DevOpsOfChaos/smarthome-technikerprojekt/docs/firmware/devices/README.md

# Devices — Übersicht

| Device | Datei | Kurzbeschreibung |
|---|---|---|
| NET-ERL-001 | [NET-ERL-001_hall_module.md](NET-ERL-001_hall_module.md) | Flurmodul (PIR, BME280, VEML7700, 1 Relais) |
| NET-ERL-002 | [NET-ERL-002_hall_module_led_ring.md](NET-ERL-002_hall_module_led_ring.md) | Erweitertes Flurmodul (LD2410 Radar, BME680, ENS160, NeoPixel-Ring, 1 Relais) |
| NET-ZRL-002 | [NET-ZRL-002_shutter_module.md](NET-ZRL-002_shutter_module.md) | Rollladenmodul (2 Relais, 3 Taster, Kalibrierung, Positionsschätzung) |
| NET-SEN-002 | [NET-SEN-002_weather_station.md](NET-SEN-002_weather_station.md) | Wettersensor (BME280, VEML7700, digitaler Regen) |
| bat_sen_01 | [bat_sen_01_window_contact.md](bat_sen_01_window_contact.md) | Batterie-Fensterkontakt (Reed, 2x AAA, GPIO-Wake) |
| bat_sen_02 | [bat_sen_02_rain_sensor.md](bat_sen_02_rain_sensor.md) | Batterie-Regensensor (ADC, Hysterese, Timer-Wake) |
