DevOpsOfChaos/smarthome-technikerprojekt/firmware/src/basetypes/master_firmware/README.md

# Master Firmware

Basistyp fuer die zentrale ESP-NOW-zu-MQTT-Bruecke.

Basis:
- Dynamische Node-Registry fuer Netz- und Batterie-Nodes
- ESP-NOW-Empfang fuer HELLO, HEARTBEAT, STATE, EVENT und ACK
- ESP-NOW-Senden fuer HELLO_ACK, STATE_REQUEST, CMD und CFG
- MQTT-Ausgabe fuer Master-Status, Node-Meta, Availability, State, Event und ACK
- MQTT-Kommandos fuer `get_state`, `set_relay`, `set_config`, `open`, `close`, `stop` und `set_position`
- Pending-/Retry-Logik fuer bestaetigungspflichtige CMD- und CFG-Nachrichten

Sichtbare MQTT-Linie:
- `smarthome/master/{DEVICE_ID}/status`
- `smarthome/master/{DEVICE_ID}/event`
- `smarthome/device/{node_id}/meta`
- `smarthome/device/{node_id}/availability`
- `smarthome/device/{node_id}/state`
- `smarthome/device/{node_id}/ack`
- `smarthome/device/{node_id}/event`
- `smarthome/device/{node_id}/command`

Hinweis:
- Zugangsdaten gehoeren nicht in diese Firmware-Dateien, sondern in die lokale `Secrets.h`.
- Der Master speichert keine feste Node-Liste; Nodes melden sich dynamisch per HELLO.
- `HELLO` ist die einzige Quelle fuer `device_class`, `power_type`, `caps` und Profile.
- Wenn zuerst nur `HEARTBEAT` oder `STATE` einer unbekannten Node eintrifft, legt der Master nur einen provisorischen Slot fuer `device_id` und MAC an, sendet `HELLO_REQUEST` und wartet. Er leitet keine Geraeteklasse aus ID-Praefixen oder Payload-Laengen ab; Availability meldet den Versorgungstyp bis zum HELLO als `unknown`.
- Batterie-Nodes duerfen laenger schlafen als Netz-Nodes. Der Master nutzt fuer BAT-SEN das gemeldete `report_interval_s`; ohne diesen Wert gilt ein konservativer Mindest-Timeout von 25min.
- NET-SEN-Regenereignisse werden zusaetzlich in den retained `state` gespiegelt (`rain`), damit ein trocken/nass-Wechsel nicht nur als fluechtiges Event sichtbar ist.
