DevOpsOfChaos/smarthome-technikerprojekt/hardware/bat_sen/devices/bat_sen_01_window_contact/gefertigte_Platine/README.md

# bat_sen_01 — KiCAD-Projekt (Geräte-Kopie)

> Kopie der Basetype-KiCAD-Dateien zur gerätespezifischen Anpassung.

## Enthaltene Platinen

| Platine | Quelle |
|---|---|
| [kicad/](.) | Sensor_Batteriebetrieb (Power-Gating, Batterie-ADC) |

## Anpassungen für bat_sen_01

- [ ] Reed-Schalter an GPIO3 (Wake-Up-fähig)
- [ ] 2x-AAA-Batteriehalter (BAT_PROFILE_2X_AAA)
- [ ] Keine I²C-Sensoren (JP1/JP2 offen)
