DevOpsOfChaos/smarthome-technikerprojekt/hardware/bat_sen/devices/bat_sen_02_rain_sensor-unfinished/kicad/README.md

# bat_sen_02 — KiCAD-Projekt (Geräte-Kopie)

> Kopie der Basetype-KiCAD-Dateien zur gerätespezifischen Anpassung.

## Enthaltene Platinen

| Platine | Quelle |
|---|---|
| [kicad/](.) | Sensor_Batteriebetrieb (Power-Gating, Batterie-ADC) |

## Anpassungen für bat_sen_02

- [ ] Analoger Regensensor an GPIO4 (ADC)
- [ ] 2× AA-Batteriehalter (BAT_PROFILE_2X_AA)
- [ ] Hysterese-Schwellwerte in Firmware
