DevOpsOfChaos/smarthome-technikerprojekt/hardware/3d_models/net_sen/link.txt

https://makerworld.com/de/models/1312159-modern-weather-station?from=search#profileId-1346594
