DevOpsOfChaos/smarthome-technikerprojekt/docs/public/01_projektueberblick.md

# Projektüberblick

## Ziel des Projekts
Dieses Projekt ist ein lokales, modulares Smart-Home-System im Rahmen eines Technikerprojekts.

Der Fokus liegt auf:
- klarer technischer Architektur
- nachvollziehbarer Trennung der Kommunikationswege
- wiederverwendbaren Basistypen
- sauber dokumentierter Entwicklung
- einem System, das technisch erklärbar und praktisch testbar bleibt
- einer nachvollziehbaren Wahl zwischen eigener Firmware und ESPHome-Alternative

## Systemidee in Kurzform
Die Hauptlinie des Gesamtsystems besteht aus drei Schichten:

1. **Dezentrale Geräte**
   - Sensor- und Aktormodule auf ESP32-Basis
   - Kommunikation mit dem Master ausschließlich per ESP-NOW

2. **Master**
   - zentrale Brücke zwischen Geräteschicht und Server
   - einzige Stelle, die ESP-NOW und MQTT verbindet

3. **Server**
   - MQTT-Ingest
   - Node-RED-basierte Verarbeitung und Visualisierung
   - Snapshot-Datenhaltung für aktuelle Zustände
   - Dashboard für Übersicht, Details und einfache Bedienung

Zusätzlich gibt es eine ESPHome-Alternative:
- Geräte werden in ESPHome/YAML beschrieben
- Home Assistant beziehungsweise ESPHome baut und flasht die Geräte
- die Geräte sprechen direkt MQTT mit dem Serververtrag
- der Node-RED-Server sieht weiterhin `meta`, `availability`, `state`, `ack` und `command`

## Grundprinzipien
Für die eigene Firmware-Linie gilt:
- Nodes sprechen nicht direkt mit dem Server.
- MQTT ist kein zweiter Gerätebus, sondern die Verbindung zwischen Master und Server.
- Der Master bleibt die einzige Brücke.
- Geräte sollen über Basistypen und Fähigkeiten sauber beschreibbar bleiben.
- Der Code soll modular sein, aber nicht unnötig abstrakt.

Für die ESPHome-Linie gilt:
- kein ESP-NOW
- kein Master
- direkte MQTT-Anbindung an denselben Serververtrag
- kompatible Topic- und Payload-Struktur statt eigener Server-Sonderlogik

## Basistypen
Aktuell folgt das Projekt dieser Basistyp-Linie:
- `master`
- `net_erl`
- `net_zrl`
- `net_sen`
- `bat_sen`

Konkrete Geräte werden auf dieser Grundlage beschrieben, statt für jedes Sondergerät eine völlig neue Serverlogik einzuziehen.

## Öffentliche Zielrichtung
Das öffentliche Repo zeigt die offizielle technische Projektlinie.
Es dient als sauberer, nachvollziehbarer und präsentierbarer Projektstand.

Wichtig ist die ehrliche Einordnung:
- Die eigene Firmware-Linie ist die Architektur-Hauptlinie des Technikerprojekts.
- Die ESPHome-Linie ist eine praktische Alternative für Anwender, die ESPHome bereits nutzen oder schneller über YAML arbeiten möchten.
- Der Serververtrag verbindet beide Welten.

## Was dieses Repo bewusst nicht sein soll
- Sammelbecken für nicht-öffentliche Projektdateien
- Experimentablage ohne klare Linie
- Ort für sensible Daten
- künstlich aufgeblähte Architektur-Spielwiese

## Nächster sinnvoller Einstieg
Für den aktuellen Serverstand anschließend lesen:
- `02_architektur_und_kommunikation.md`
- `03_aktueller_status_und_naechste_schritte.md`
- `18_firmware_oder_esphome.md`
- `04_server_schnellstart_phase1.md`
