DevOpsOfChaos/smarthome-technikerprojekt/docs/ausarbeitung/nachweise/screenshots/overview_desktop-1440x900.png

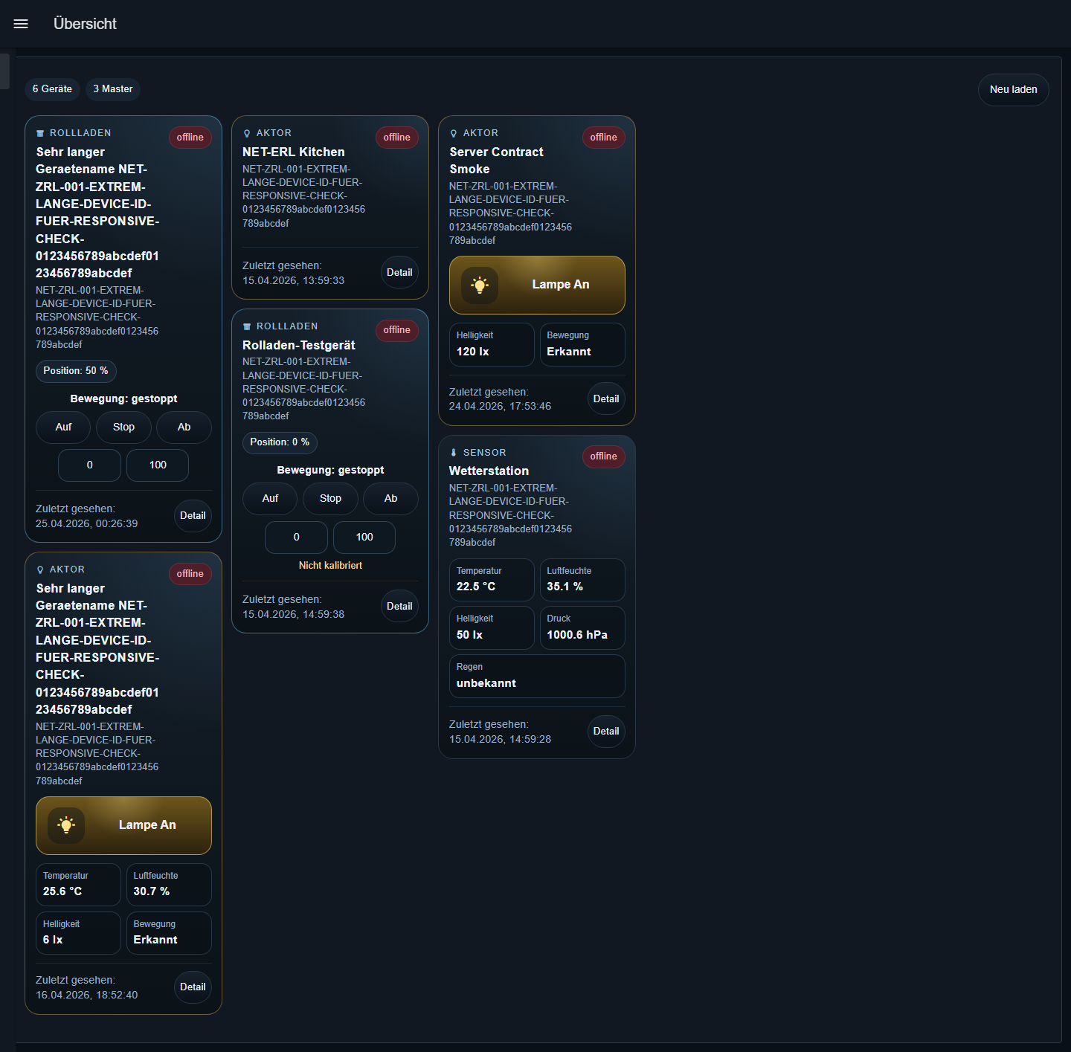
docs/ausarbeitung/nachweise/screenshots/overview_desktop-1440x900.png
