DevOpsOfChaos/smarthome-technikerprojekt/hardware/3d_models/bat_sen/pictures/_frames/gif1/f0020.png

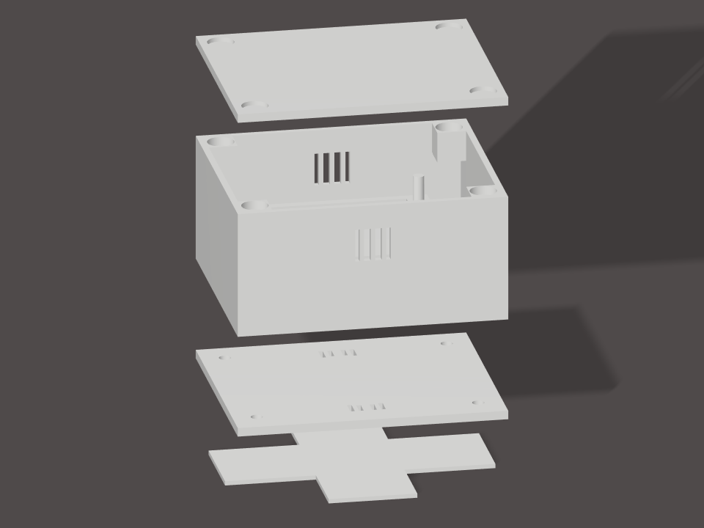
hardware/3d_models/bat_sen/pictures/_frames/gif1/f0020.png
