DevOpsOfChaos/smarthome-technikerprojekt/hardware/3d_models/bat_sen/pictures/_frames/gif1/f0062.png

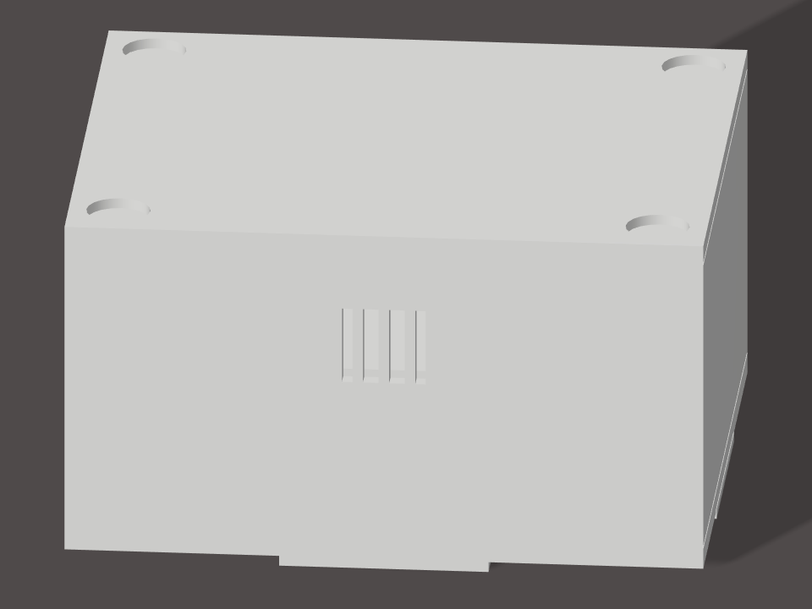
hardware/3d_models/bat_sen/pictures/_frames/gif1/f0062.png
