DevOpsOfChaos/smarthome-technikerprojekt/hardware/3d_models/bat_sen/pictures/_frames/gif2/f0021.png

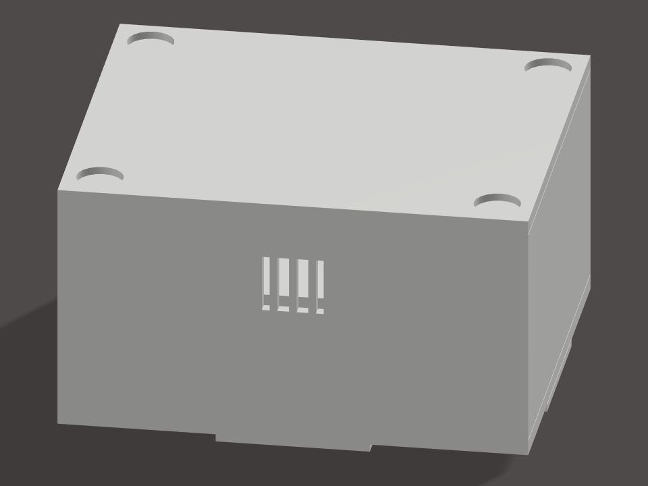
hardware/3d_models/bat_sen/pictures/_frames/gif2/f0021.png
