DevOpsOfChaos/smarthome-technikerprojekt/hardware/3d_models/bat_sen/pictures/_frames/gif3/f0038.png

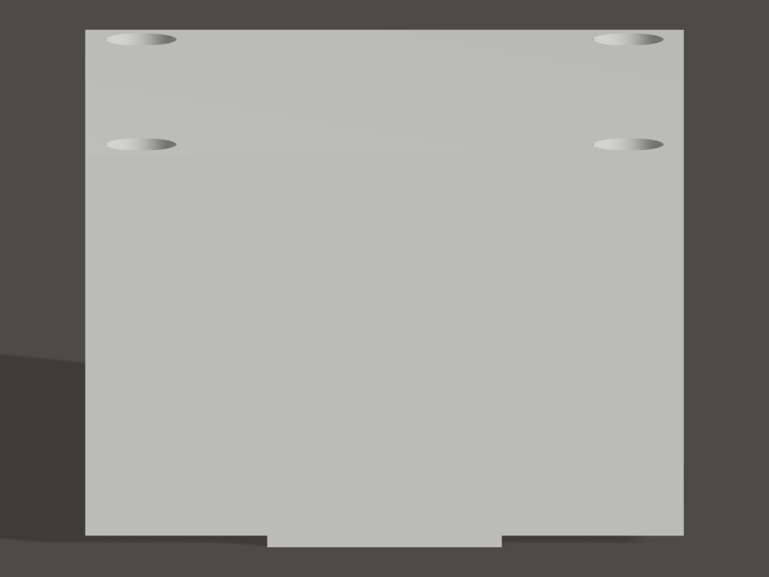
hardware/3d_models/bat_sen/pictures/_frames/gif3/f0038.png
