DevOpsOfChaos/smarthome-technikerprojekt/hardware/3d_models/bat_sen/pictures/_frames/gif3/f0046.png

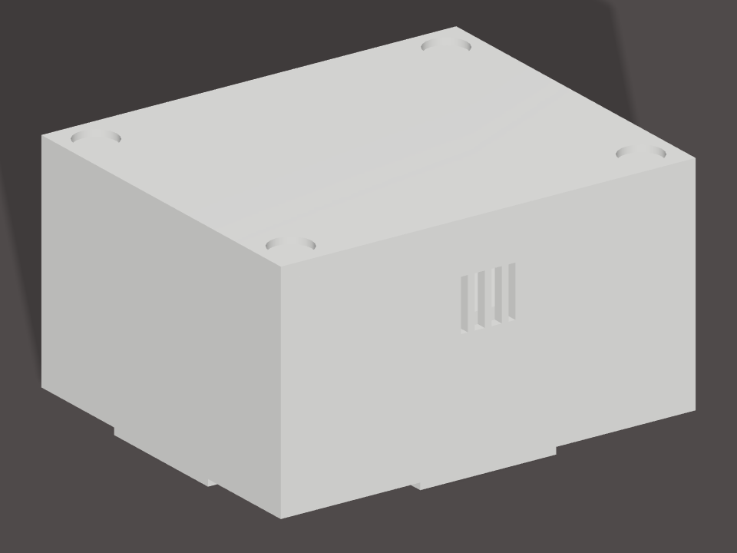
hardware/3d_models/bat_sen/pictures/_frames/gif3/f0046.png
