DevOpsOfChaos/smarthome-technikerprojekt/hardware/3d_models/net_erl/pictures/with_led_ring/06_Diffusor_WarmWeiss.png

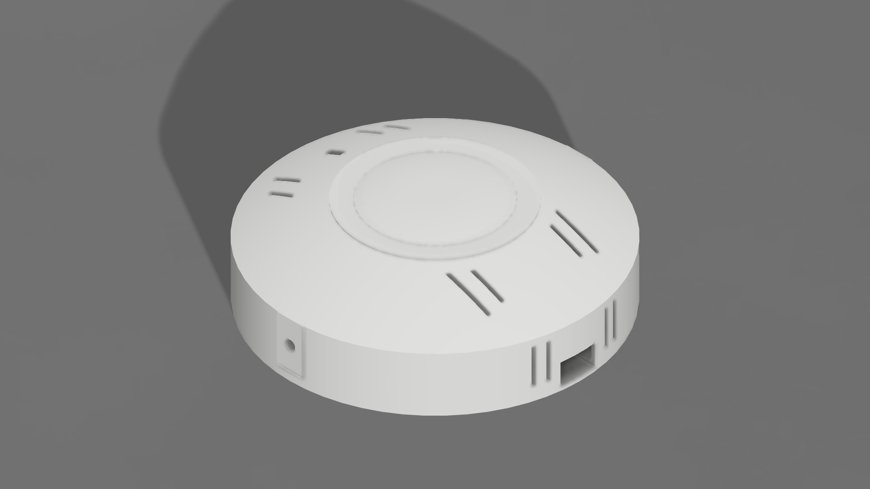
hardware/3d_models/net_erl/pictures/with_led_ring/06_Diffusor_WarmWeiss.png
