DevOpsOfChaos/smarthome-technikerprojekt/hardware/3d_models/net_erl/pictures/with_led_ring/gif/1/frame_032.png

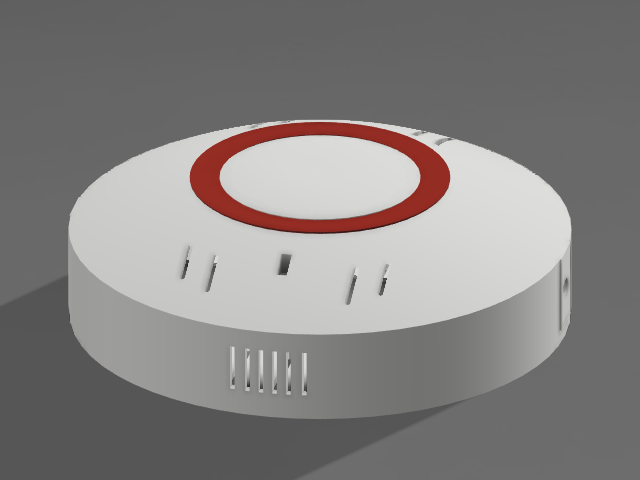
hardware/3d_models/net_erl/pictures/with_led_ring/gif/1/frame_032.png
