DevOpsOfChaos/smarthome-technikerprojekt/hardware/3d_models/net_erl/pictures/with_led_ring/gif/2/explode_022.png

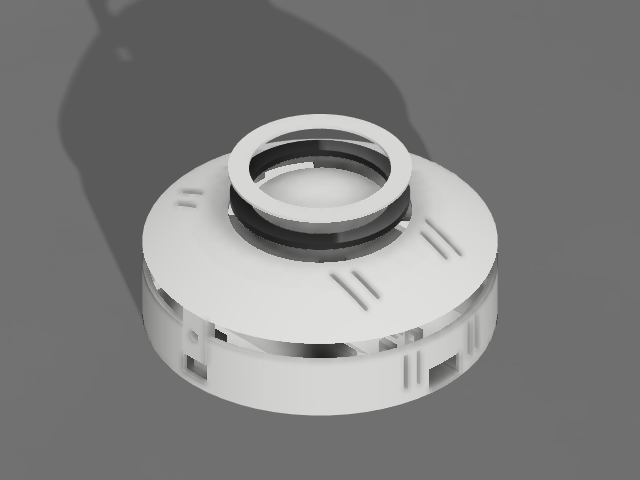
hardware/3d_models/net_erl/pictures/with_led_ring/gif/2/explode_022.png
