DevOpsOfChaos/smarthome-technikerprojekt/hardware/3d_models/net_erl/pictures/with_led_ring/gif/3/explode_003.png

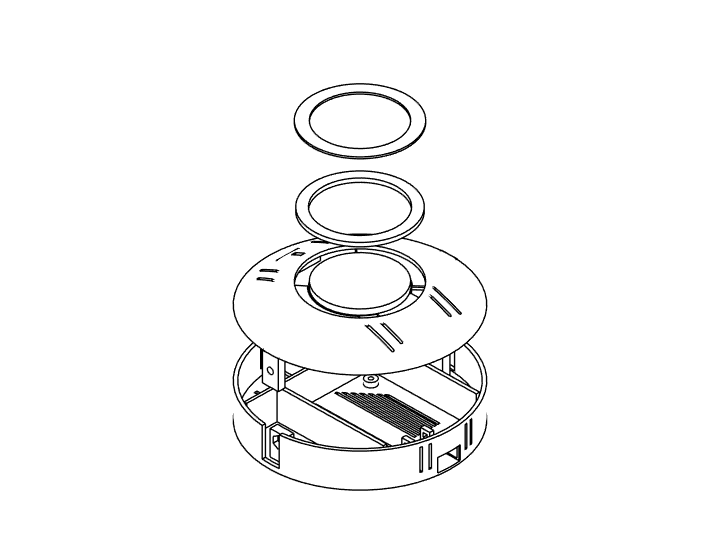
hardware/3d_models/net_erl/pictures/with_led_ring/gif/3/explode_003.png
