DevOpsOfChaos/smarthome-technikerprojekt/hardware/3d_models/net_erl/pictures/with_led_ring/gif/3/explode_044.png

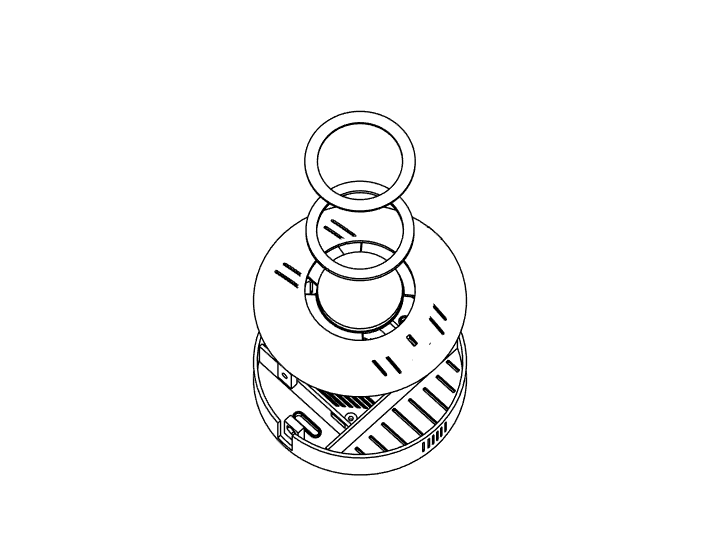
hardware/3d_models/net_erl/pictures/with_led_ring/gif/3/explode_044.png
