DevOpsOfChaos/smarthome-technikerprojekt/hardware/3d_models/net_erl/pictures/with_pir/2/gif1_frame_031.png

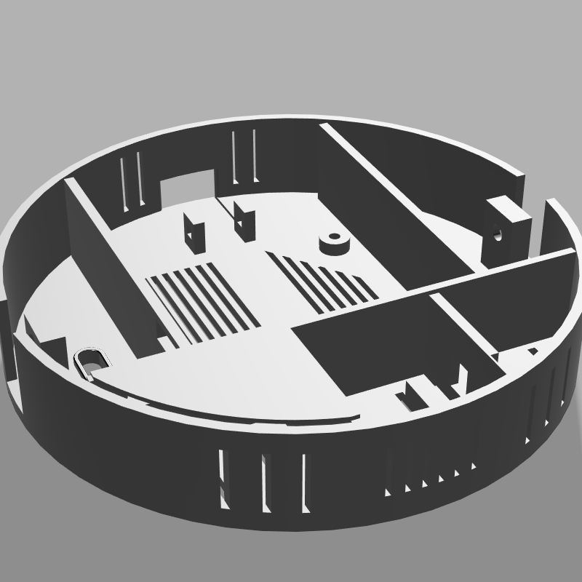
hardware/3d_models/net_erl/pictures/with_pir/2/gif1_frame_031.png
