DevOpsOfChaos/smarthome-technikerprojekt/hardware/3d_models/net_erl/pictures/with_pir/2/gif2_frame_012.png

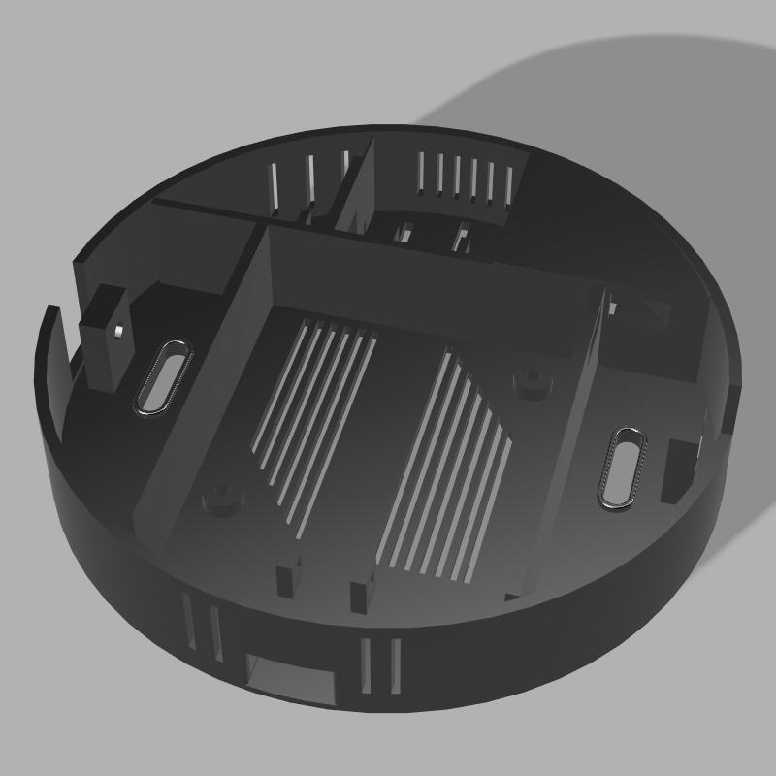
hardware/3d_models/net_erl/pictures/with_pir/2/gif2_frame_012.png
