DevOpsOfChaos/smarthome-technikerprojekt/hardware/3d_models/net_erl/pictures/with_pir/2/gif3_frame_027.png

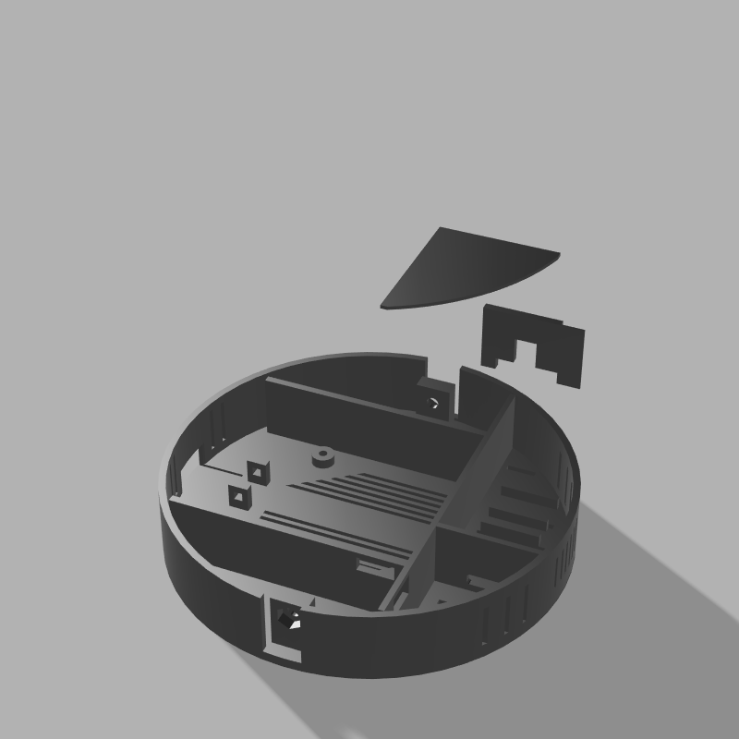
hardware/3d_models/net_erl/pictures/with_pir/2/gif3_frame_027.png
