DevOpsOfChaos/smarthome-technikerprojekt/hardware/3d_models/net_erl/pictures/with_pir/2/gif3_frame_069.png

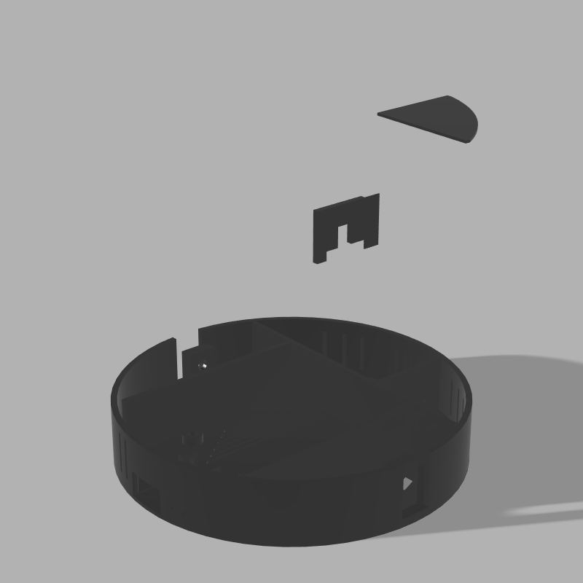
hardware/3d_models/net_erl/pictures/with_pir/2/gif3_frame_069.png
