DevOpsOfChaos/smarthome-technikerprojekt/hardware/3d_models/net_erl/pictures/with_pir/gif1_frame_065.png

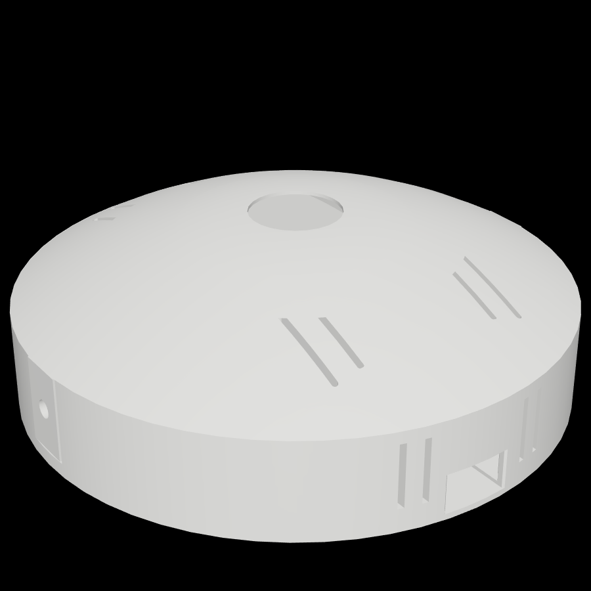
hardware/3d_models/net_erl/pictures/with_pir/gif1_frame_065.png
