DevOpsOfChaos/smarthome-technikerprojekt/hardware/3d_models/net_erl/pictures/with_pir/gif1_rotation_360.gif

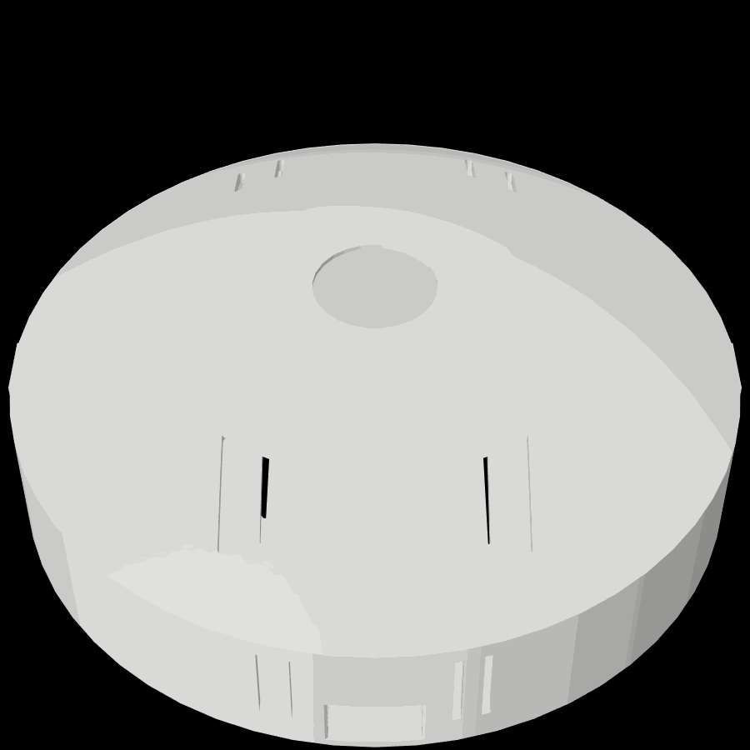
hardware/3d_models/net_erl/pictures/with_pir/gif1_rotation_360.gif
