DevOpsOfChaos/smarthome-technikerprojekt/hardware/3d_models/net_erl/pictures/with_pir/gif2_frame_052.png

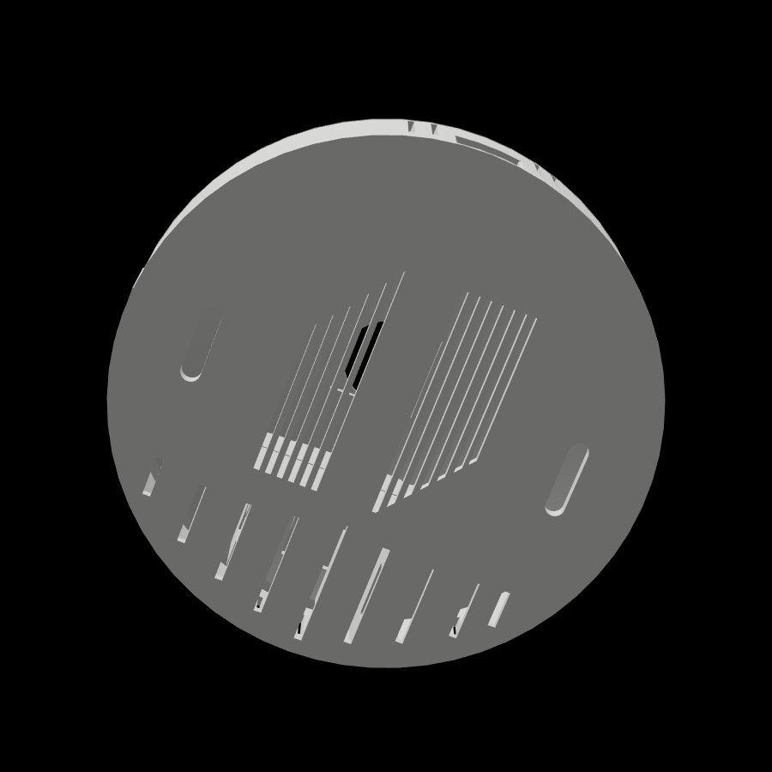
hardware/3d_models/net_erl/pictures/with_pir/gif2_frame_052.png
