DevOpsOfChaos/smarthome-technikerprojekt/hardware/3d_models/net_erl/pictures/with_pir/gif2_top_to_bottom.gif

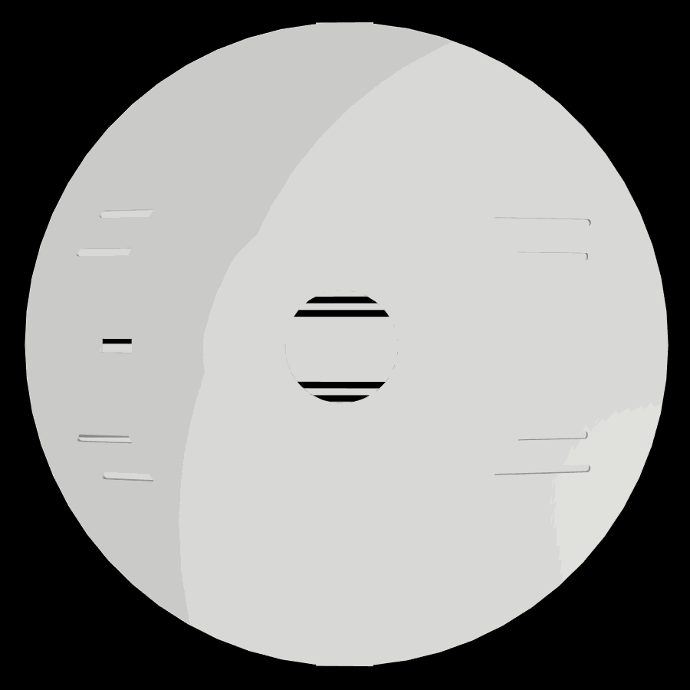
hardware/3d_models/net_erl/pictures/with_pir/gif2_top_to_bottom.gif
