DevOpsOfChaos/smarthome-technikerprojekt/hardware/3d_models/net_zrl/pictures/gif_360/frame_024.png

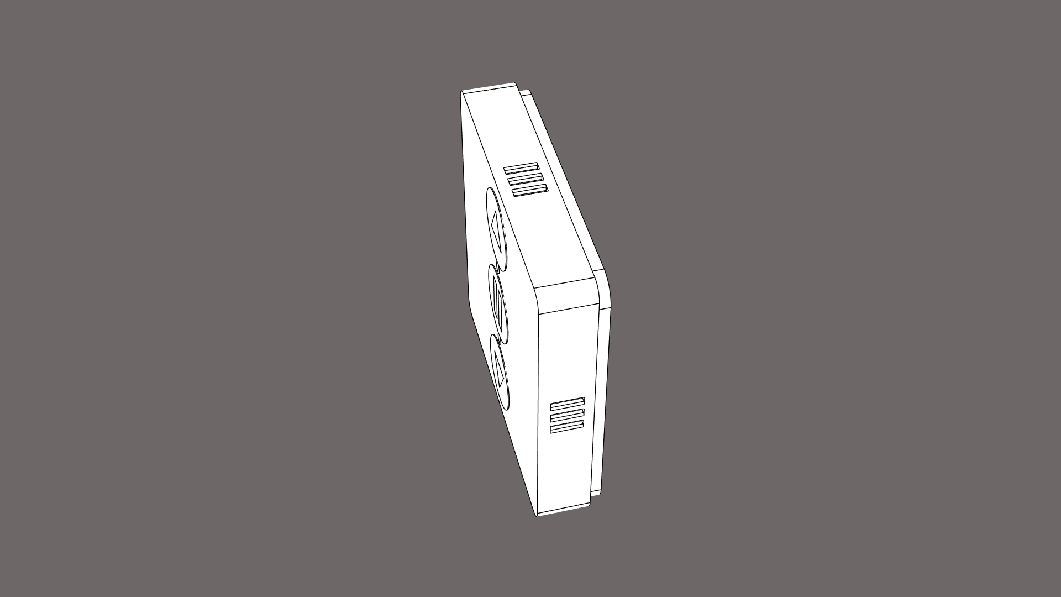
hardware/3d_models/net_zrl/pictures/gif_360/frame_024.png
