DevOpsOfChaos/smarthome-technikerprojekt/hardware/3d_models/net_zrl/pictures/gif_explosion/frame_041.png

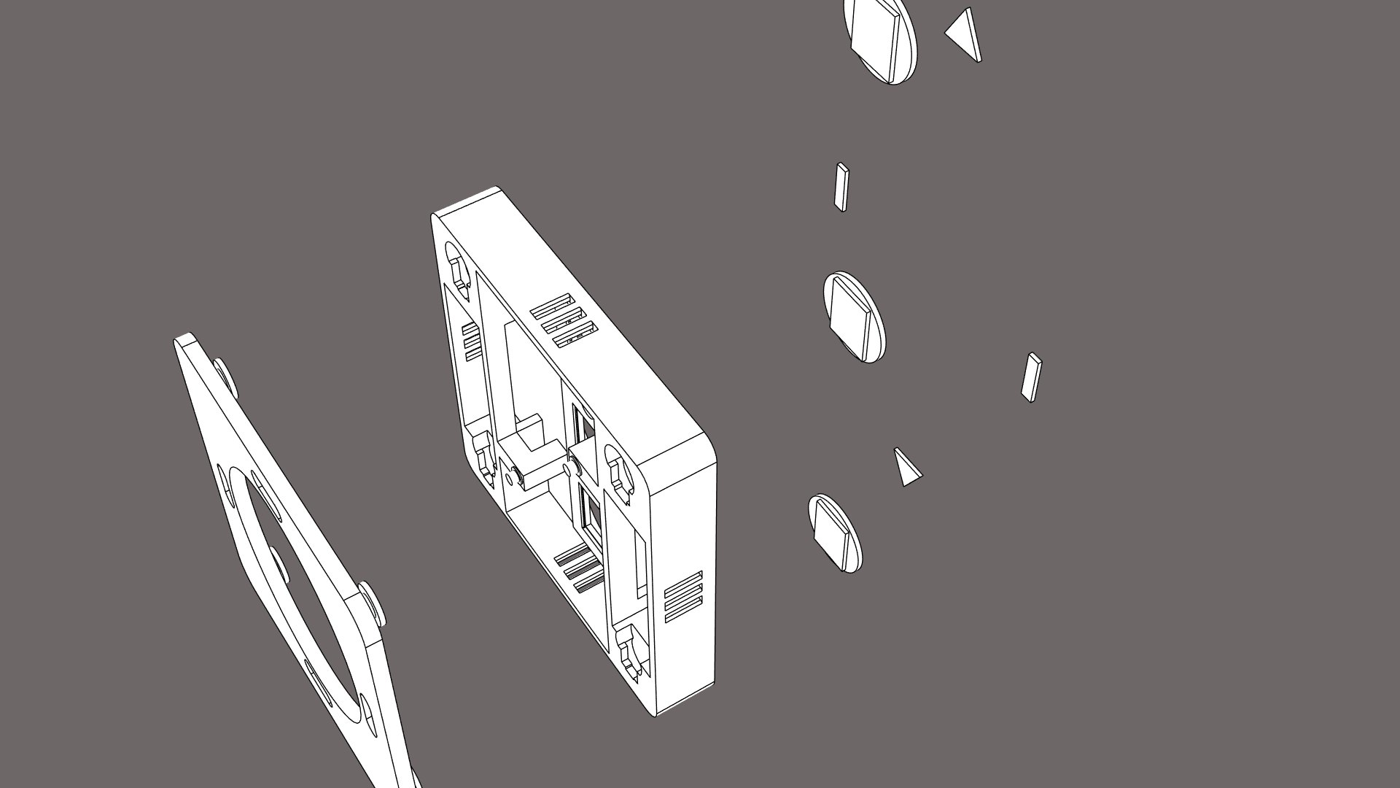
hardware/3d_models/net_zrl/pictures/gif_explosion/frame_041.png
