DevOpsOfChaos/smarthome-technikerprojekt/hardware/3d_models/net_zrl/pictures/gif_product/frame_019.png

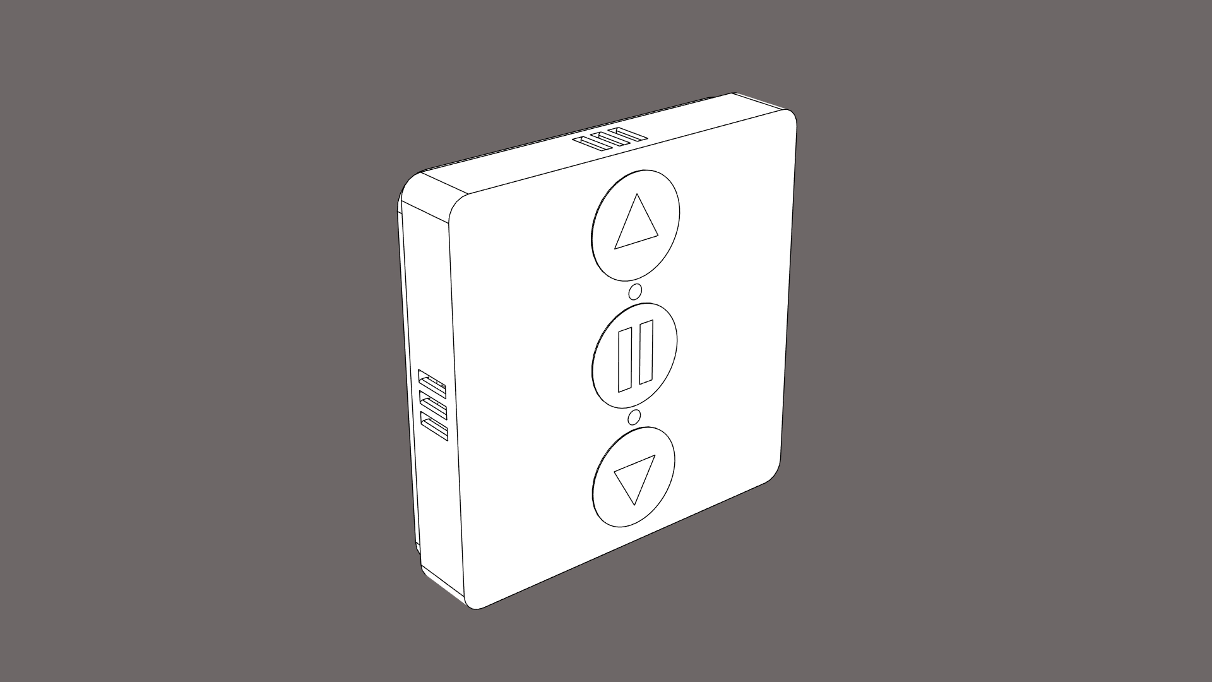
hardware/3d_models/net_zrl/pictures/gif_product/frame_019.png
