DevOpsOfChaos/smarthome-technikerprojekt/hardware/3d_models/net_zrl/pictures/gif_product/frame_070.png

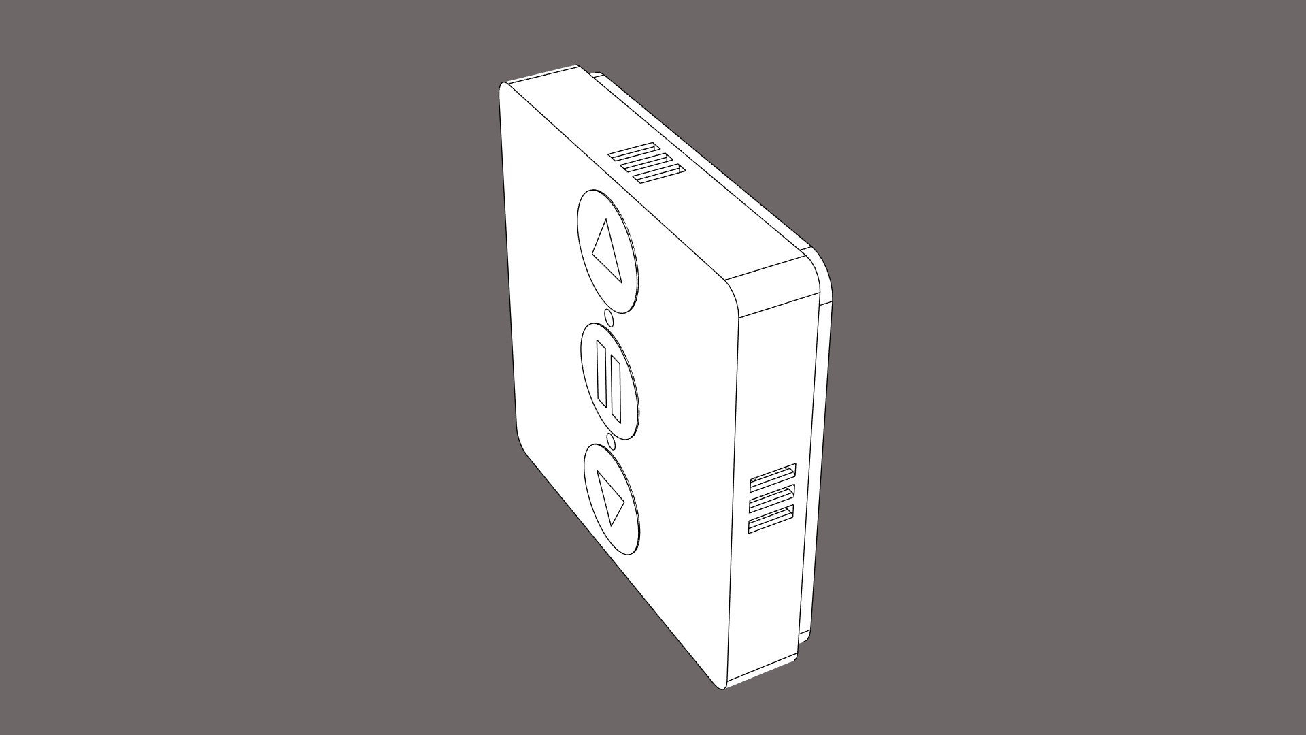
hardware/3d_models/net_zrl/pictures/gif_product/frame_070.png
