DevOpsOfChaos/smarthome-technikerprojekt/hardware/3d_models/net_erl/Trennwand.3mf

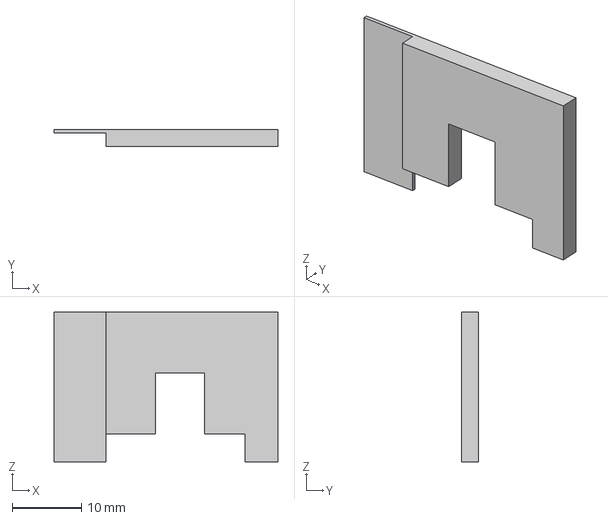
[picture p203: CAD file, 2026-05-26]
hardware/3d_models/net_erl/Trennwand.3mf
32.3 x 2.50 x 21.6 mm
