DevOpsOfChaos/smarthome-technikerprojekt/hardware/3d_models/net_zrl/BODY_FRONT_CONTROL_BASE_V2.3mf

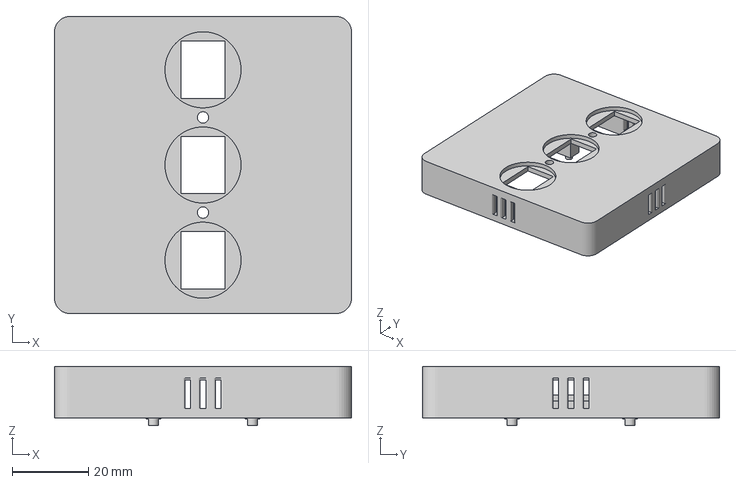
[picture p204: CAD file, 2026-05-26]
hardware/3d_models/net_zrl/BODY_FRONT_CONTROL_BASE_V2.3mf
78.0 x 78.0 x 15.5 mm
