DevOpsOfChaos/smarthome-technikerprojekt/hardware/3d_models/net_erl/Deckel_PIR.3mf

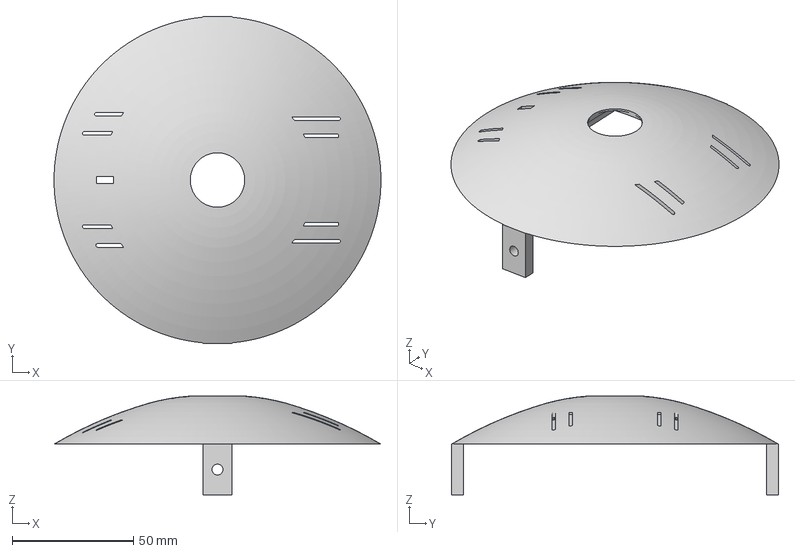
[picture p205: CAD file, 2026-05-26]
hardware/3d_models/net_erl/Deckel_PIR.3mf
134.9 x 135.0 x 40.9 mm
