DevOpsOfChaos/smarthome-technikerprojekt/hardware/3d_models/net_zrl/buttons.3mf

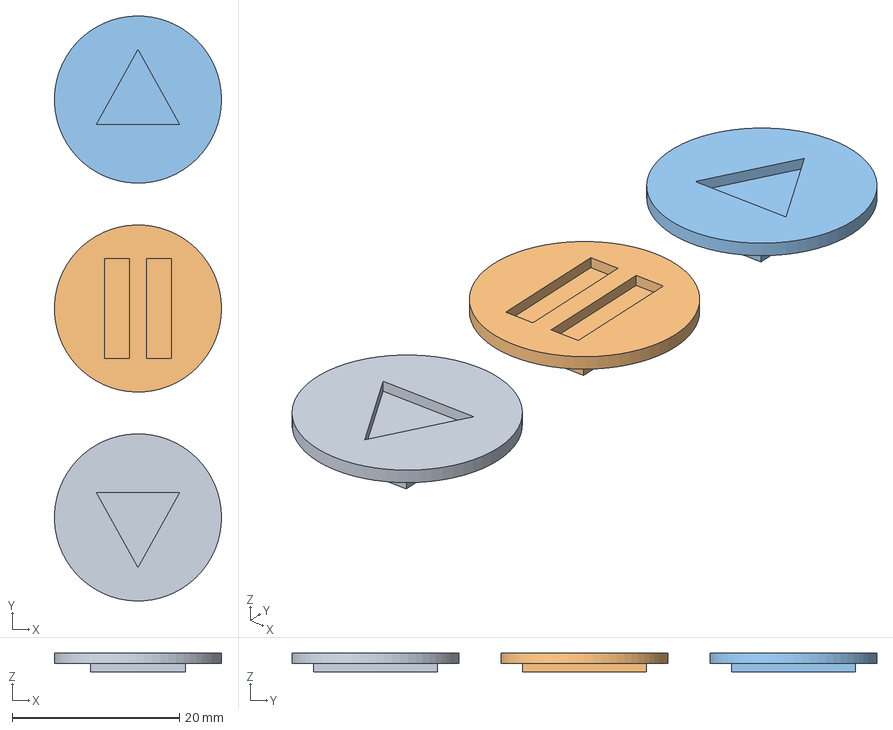
[picture p207: CAD file, 2026-05-26]
hardware/3d_models/net_zrl/buttons.3mf
20.0 x 70.0 x 2.25 mm
Button_down
Button_middle
Button_up
