DevOpsOfChaos/smarthome-technikerprojekt/hardware/shared/modularer_steuerkreis/steuerkreis.kicad_sch

## KiCad design hardware/shared/modularer_steuerkreis/steuerkreis.kicad_sch (2026-05-25)

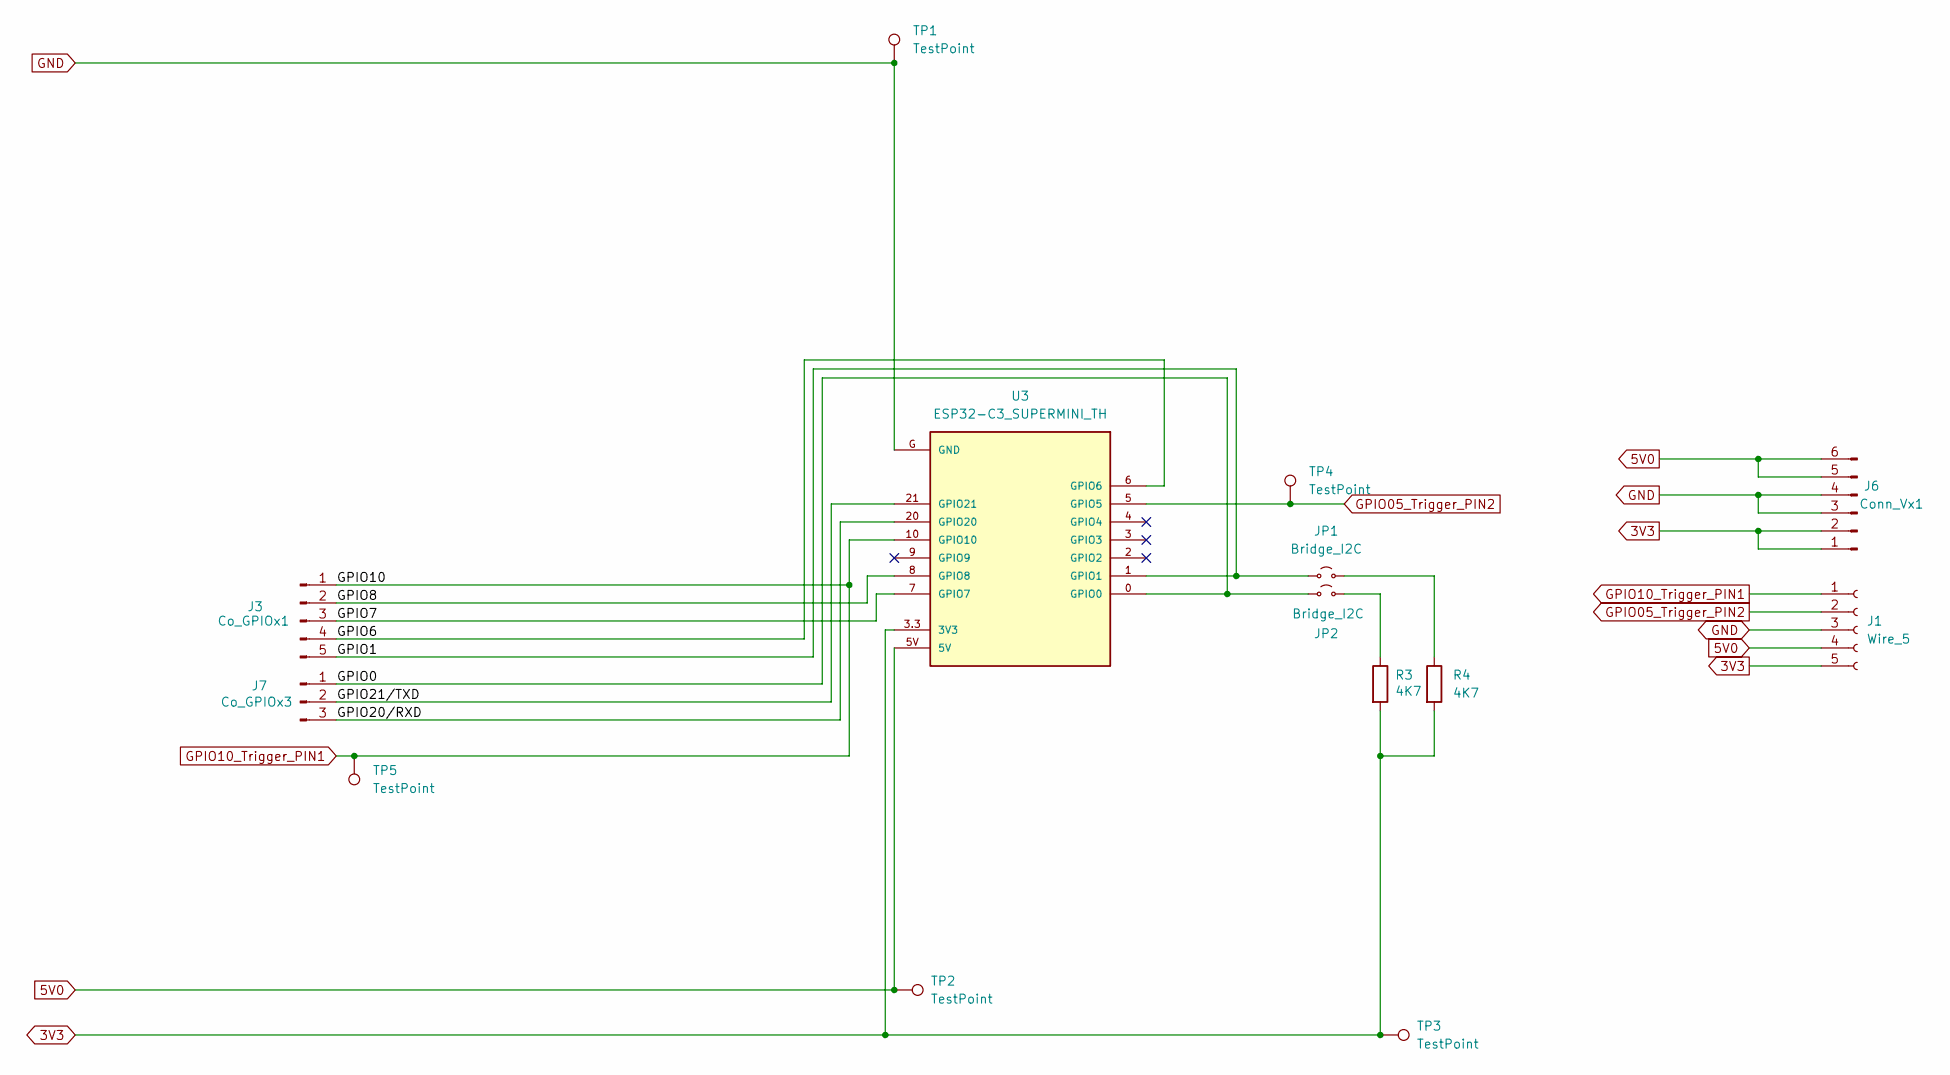
[picture p217: schematic steuerkreis.kicad_sch]

Parts:
J1: Wire_5; SolderWire-0.25sqmm_1x05_P4.2mm_D0.65mm_OD1.7mm
J3: Co_GPIOx1; PinHeader_1x05_P2.54mm_Vertical
J6: Conn_Vx1; PinHeader_1x06_P2.54mm_Vertical
J7: Co_GPIOx3; PinHeader_1x03_P2.54mm_Vertical
JP1, JP2: Bridge_I2C; SolderJumper-2_P1.3mm_Open_Pad1.0x1.5mm
R3, R4: 4K7; R_0805_2012Metric_Pad1.20x1.40mm_HandSolder
TP1, TP2, TP3, TP4, TP5: TestPoint; TestPoint_Pad_D1.0mm
U3: ESP32-C3_SUPERMINI_TH; MODULE_ESP32-C3_SUPERMINI_TH

Connections:
3V3: J1.5, J6.1, J6.2, R3.2, R4.2, TP3.1, U3.3.3 (3V3)
5V0: J1.4, J6.5, J6.6, TP2.1, U3.5V
GND: J1.3, J6.3, J6.4, TP1.1, U3.G (GND)
GPIO0: J7.1, JP2.1 (A), U3.0 (GPIO0)
GPIO1: J3.5, JP1.1 (A), U3.1 (GPIO1)
GPIO05_Trigger_PIN2: J1.2, TP4.1, U3.5 (GPIO5)
GPIO6: J3.4, U3.6 (GPIO6)
GPIO7: J3.3, U3.7 (GPIO7)
GPIO8: J3.2, U3.8 (GPIO8)
GPIO10_Trigger_PIN1: J1.1, J3.1, TP5.1, U3.10 (GPIO10)
GPIO20/RXD: J7.3, U3.20 (GPIO20)
GPIO21/TXD: J7.2, U3.21 (GPIO21)
unnamed: JP1.2 (B), R4.1
unnamed: JP2.2 (B), R3.1
