DevOpsOfChaos/smarthome-technikerprojekt/esphome/devices/net_zrl_shutter_module.yaml

# =============================================================================
# net_zrl_shutter_module.yaml
# =============================================================================
# Projekt:    Smarthome Technikerprojekt – alternative MQTT-Linie
# Zweck:      MQTT-basierte Alternativ-Firmware für Smarthome-Geraete
# Lizenz:     Proprietär – nur für Projektzwecke
# Pfad:       devices/net_zrl_shutter_module.yaml
#
# Datei-Funktion:
#   Beispiel: Netzbetriebener Rollladen mit 2 Relais (auf/ab) und
#   zeitbasierter Positionssteuerung. Enthaelt Kalibrierungs-Unterstuetzung
#   fuer automatische Fahrzeit-Messung und prozentuale Teil-Positionierung.
#   Nutzt die Cover-Contracts aus smarthome_cover_contract.yaml.
#
# MQTT-Topics:
#   smarthome/device/{device_id}/meta         – Geraete-Metadaten
#   smarthome/device/{device_id}/availability – Online/Offline
#   smarthome/device/{device_id}/state        – Cover-Status (cover_state,
#                                                cover_position, cover_calibrated, fault)
#   smarthome/device/{device_id}/ack          – Kommando-Bestaetigung
#   smarthome/device/{device_id}/command      – Eingehende Kommandos
#
# Autor:           DevOpsOfChaos
# Erstelldatum:    2026-05-14
# Letzte Änderung: 2026-05-14
#
# Aenderungshistorie:
#   [2026-05-14] DevOpsOfChaos – Initiale Erstellung
#
# Abhaengigkeiten:
#   Importiert: smarthome_contract_base.yaml
#              smarthome_command_ack.yaml
#              smarthome_cover_contract.yaml
#   Wird importiert von: (keine – Device-Datei)
# =============================================================================

# =============================================================================
# SUBSTITUTIONS – Geraete-Pins und Konfiguration
# =============================================================================
# caps="10243" → RELAY(1) + RELAY2(2) + MULTIBUTTON(2048) + COVER(8192)
# control_mode="cover", config_profile="cover_basic"
substitutions:
  node_name: net-zrl-020
  device_id: NET-ZRL-020
  device_name: NET-ZRL Shutter
  device_class: net_zrl
  power_type: mains
  fw_version: "1"
  caps: "10243" # Bitmaske: RELAY(1)|RELAY2(2)|MULTIBUTTON(2048)|COVER(8192)
  meta_schema_version: "1"
  control_mode: cover
  config_profile: cover_basic
  reporting_mode: hybrid
  sensor_mask: XXXXXXXXXX
  input_mask: XXXXX
  setup_ap_password: net-zrl-setup
  setup_status_default: "60"
  setup_sensor_default: "60"
  setup_status_min: "10"
  setup_status_max: "65535"
  setup_sensor_min: "10"
  setup_sensor_max: "65535"
  relay_up_pin: GPIO10               # bestehende Firmware: NET_ZRL_RELAY_UP_PIN
  relay_down_pin: GPIO5              # bestehende Firmware: NET_ZRL_RELAY_DOWN_PIN
  default_cover_travel_ms: "100000" # 100000 ms = 100 s Standard-Fahrzeit
  button_up_pin: GPIO20
  button_down_pin: GPIO4
  button_stop_pin: GPIO3
  led_up_pin: GPIO7
  led_down_pin: GPIO6

# =============================================================================
# PACKAGES – Eingebundene Contract-Bausteine
# =============================================================================
packages:
  contract_base: !include ../packages/smarthome_contract_base.yaml
  command_ack: !include ../packages/smarthome_command_ack.yaml
  cover_contract: !include ../packages/smarthome_cover_contract.yaml
  device_event: !include ../packages/smarthome_device_event.yaml

# =============================================================================
# BASIS – Basis-Konfiguration und Boot-Verhalten
# =============================================================================
esphome:
  name: ${node_name}
  friendly_name: ${device_name}
  includes:
    - ../packages/setup_portal.h
    - ../packages/smarthome_command_dispatch.h
  comment: Vertragskompatibles MQTT-Cover mit Kalibrierung und Positionssteuerung
  on_boot:
    priority: -10
    then:
      - lambda: |-
          id(contract_online) = true;
          id(cover_contract_state) = "stopped";
          id(cover_contract_calibrated) =
            id(cover_contract_travel_up_ms) >= 1000 &&
            id(cover_contract_travel_down_ms) >= 1000;
          if (!id(cover_contract_calibrated)) {
            id(cover_contract_travel_up_ms) = 0;
            id(cover_contract_travel_down_ms) = 0;
            id(cover_contract_position) = 255;
          }
      - script.execute: apply_setup_sensor_interval
      - script.execute: publish_contract_meta
      - script.execute: publish_contract_availability
      - script.execute: publish_cover_contract_state
      - script.execute: publish_boot_event

esp32:
  board: esp32-c3-devkitm-1
  toolchain: platformio
  framework:
    type: arduino

logger:
  level: DEBUG

wifi:
  ssid: !secret wifi_ssid
  password: !secret wifi_password
  ap:
    ssid: ${node_name}-setup
    password: ${setup_ap_password}

# =============================================================================
# MQTT – Verbindungsaufbau, Birth/Will, Connect/Disconnect
# =============================================================================
mqtt:
  broker: !secret mqtt_broker
  username: !secret mqtt_username
  password: !secret mqtt_password
  topic_prefix: smarthome/device/${device_id}/internal
  discovery: false
  log_topic: null
  shutdown_message: null
  birth_message:
    topic: smarthome/device/${device_id}/availability
    retain: true
    payload: '{"device_id":"${device_id}","availability":"online","online":true,"power_type":"${power_type}"}'
  will_message:
    topic: smarthome/device/${device_id}/availability
    retain: true
    payload: '{"device_id":"${device_id}","availability":"offline","online":false,"power_type":"${power_type}"}'
  on_connect:
    then:
      - lambda: |-
          id(contract_online) = true;
          if (id(setup_portal_active)) {
            SmartHomeSetupPortal::stop();
            id(setup_portal_active) = false;
          }
      - script.execute: publish_contract_meta
      - script.execute: publish_contract_availability
      - script.execute: publish_cover_contract_state
  on_disconnect:
    then:
      - lambda: |-
          id(contract_online) = false;
      - script.execute: publish_contract_availability

# =============================================================================
# SWITCH – Zwei GPIO-Relais (Auf/Ab) mit ALWAYS_OFF (Start immer aus)
# =============================================================================
switch:
  - platform: gpio
    id: cover_relay_up
    pin: ${relay_up_pin}
    restore_mode: ALWAYS_OFF
    name: "Cover Relay Up"
    on_turn_on:
      then:
        - switch.turn_on: cover_led_up
    on_turn_off:
      then:
        - switch.turn_off: cover_led_up
  - platform: gpio
    id: cover_relay_down
    pin: ${relay_down_pin}
    restore_mode: ALWAYS_OFF
    name: "Cover Relay Down"
    on_turn_on:
      then:
        - switch.turn_on: cover_led_down
    on_turn_off:
      then:
        - switch.turn_off: cover_led_down
  - platform: gpio
    id: cover_led_up
    pin: ${led_up_pin}
    restore_mode: ALWAYS_OFF
    name: "Cover LED Up"
    internal: true
  - platform: gpio
    id: cover_led_down
    pin: ${led_down_pin}
    restore_mode: ALWAYS_OFF
    name: "Cover LED Down"
    internal: true
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
