DevOpsOfChaos/smarthome-technikerprojekt/firmware/src/devices/net_erl_hall_light/main.cpp

/**
 * @file main.cpp
 * @brief NET-ERL Hall Light: Flurlicht mit PIR + Lux (Thin-Wrapper)
 *
 * @details Auto-Light-Logik mit PIR-Bewegungssensor und VEML7700-Luxsensor.
 *          BME280 fuer Temperatur/Feuchte. Late-Lux: Auto-On-Entscheidung
 *          wird verzoegert bis der erste Lux-Wert vorliegt.
 *          Nachlauf wird NICHT durch erneute Bewegung verlaengert.
 *
 * Hardware:   ESP32-C3 + BME280 + VEML7700 + PIR + 1 Relais
 * Pattern:    Thin-Wrapper – Hooks in NetErlRuntime.h eingehängt
 *
 * @author DevOpsOfChaos
 * @date   2026-05-14
 */

#include <Arduino.h>
#include <Wire.h>
#include <Adafruit_BME280.h>
#include <Adafruit_VEML7700.h>

#include "DeviceConfig.h"
#include "PinConfig.h"

// -- Baukasten-Defines (vor NetErlRuntime.h) --
#define NET_ERL_STORAGE_NS              "net_erl_hl"
#define NET_ERL_SENSOR_MASK             "THLMXXXXXX"
#define NET_ERL_INPUT_MASK              "XXXXX"
#define NET_ERL_PERSISTED_MAGIC         0x484C4C31UL
#define NET_ERL_PERSISTED_KEY           "hall_setup_v1"
#define NET_ERL_DEVICE_PAGE_TITLE       "NET-ERL Hall Light"
#define NET_ERL_DEVICE_SECTION_TITLE    "Hall Light"
#define NET_ERL_DEVICE_SECTION_INTRO    "Lux-Schwelle und Nachlauf."

// Hall-spezifische Unterschiede zum Kitchen
#define NET_ERL_USE_ISR_CMD_QUEUE       1   // ISR-safe CMD-Queue
#define NET_ERL_OFF_TIMER_EXTENDS_ON_MOTION 0  // Nachlauf NICHT verlängern
#define NET_ERL_WDT_TIMEOUT_S           8UL

// -- Hooks aktivieren --
#define NET_ERL_DEVICE_HAS_CUSTOM_HOOKS 1

// =============================================================================
// RUNTIME (Baukasten Block 3 – liefert setup() und loop())
// =============================================================================
#include "../../basetypes/net_erl/NetErlRuntime.h"

// =============================================================================
// DEVICE-SPEZIFISCHE OBJEKTE
// =============================================================================

Adafruit_BME280 bme280;
Adafruit_VEML7700 veml7700 = Adafruit_VEML7700();

// =============================================================================
// DEVICE-SPEZIFISCHER ZUSTAND
// =============================================================================
namespace {
    bool bme280_ok = false, veml7700_ok = false;
    unsigned long letzter_bme_recovery_ms = 0, letzter_veml_recovery_ms = 0;
    unsigned long letztes_env_sample_ms = 0;
    unsigned long veml7700_bereit_seit_ms = 0;

    // Sensor-Messwerte
    int16_t temp_01c = INT16_MIN;
    uint16_t hum_01pct = 0xFFFFU, lux = 0xFFFFU;
    bool pir_raw = false;

    constexpr uint32_t SENSOR_POLL_INTERVAL_MS = 250UL;
}

// =============================================================================
// SENSOR-HILFSFUNKTIONEN (device-spezifisch)
// =============================================================================
namespace {
    /** @brief Initialisiert BME280 an konfigurierter I2C-Adresse. @return true bei Erfolg */
    bool initBme280() {
        const uint8_t addrs[] = {(uint8_t)NET_ERL_BME280_ADDRESS};
        for (uint8_t a : addrs) {
            if (!bme280.begin(a, &Wire)) continue;
            return true;
        }
        return false;
    }

    /** @brief Konfiguriert VEML7700: Gain 1x, Integrationszeit 100ms. */
    void konfVeml7700() {
        veml7700.setGain(VEML7700_GAIN_1);
        veml7700.setIntegrationTime(VEML7700_IT_100MS);
    }

    /**
     * @brief Initialisiert VEML7700 und merkt Zeitstempel der Bereitschaft.
     * @param jetzt aktueller millis()-Wert
     * @return true bei Erfolg
     */
    bool initVeml7700(unsigned long jetzt) {
        if (!veml7700.begin()) return false;
        konfVeml7700();
        veml7700_bereit_seit_ms = jetzt;
        return true;
    }
}

// =============================================================================
// CUSTOM HOOKS (von NetErlRuntime.h aufgerufen)
// =============================================================================

/**
 * @brief Initialisiert I2C-Bus, BME280, VEML7700 und PIR-Pin.
 * Wird einmalig von NetErlRuntime beim Boot aufgerufen.
 */
void netErlDeviceInit() {
    Wire.begin(PIN_SENSOR_SDA, PIN_SENSOR_SCL);

    bme280_ok = initBme280();
    if (!bme280_ok) logMsg("WARN", "BME280 init fail");

    veml7700_ok = initVeml7700(millis());
    if (!veml7700_ok) logMsg("WARN", "VEML7700 init fail");

    pinMode(PIN_PIR, INPUT);
}

/** @brief Setzt alle Sensorwerte auf UNGUELTIG (INT16_MIN / 0xFFFF). */
void netErlDeviceResetSensorDefaults() {
    temp_01c = INT16_MIN; hum_01pct = 0xFFFFU; lux = 0xFFFFU;
}

/**
 * @brief Liest PIR-Sensor (digitalRead) und aktualisiert pir_raw.
 * @return true wenn Bewegung erkannt (HIGH)
 */
bool netErlDeviceReadPresence() {
    pir_raw = (digitalRead(PIN_PIR) == HIGH);
    return pir_raw;
}

/**
 * @brief Setzt Relais-Ausgang und optionale Status-LED.
 * @param on true = Relais aktiv
 */
void netErlDeviceSetRelayOutput(bool on) {
    digitalWrite(PIN_RELAY_1, on == RELAY_1_ACTIVE_HIGH ? HIGH : LOW);
#if PIN_STATUS_LED >= 0
    digitalWrite(PIN_STATUS_LED, on ? HIGH : LOW);
#endif
}
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
